GMM-7550/gmm7550-hardware/doc/gmm7550_preview_side_2022-03-09.png

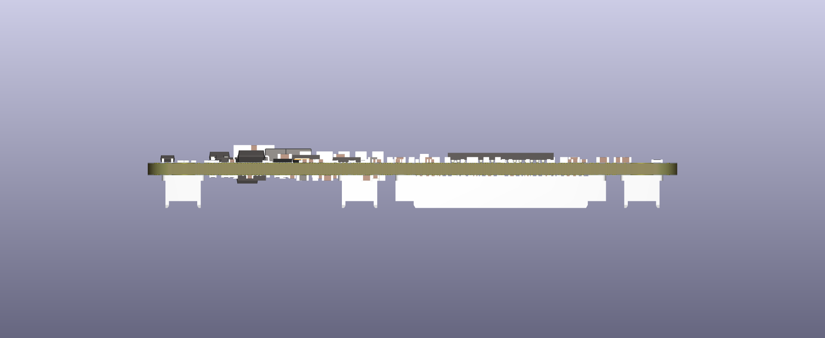
doc/gmm7550_preview_side_2022-03-09.png
