GMM-7550/gmm7550-hardware/doc/GMM-7550_preview_2020-10-01.png

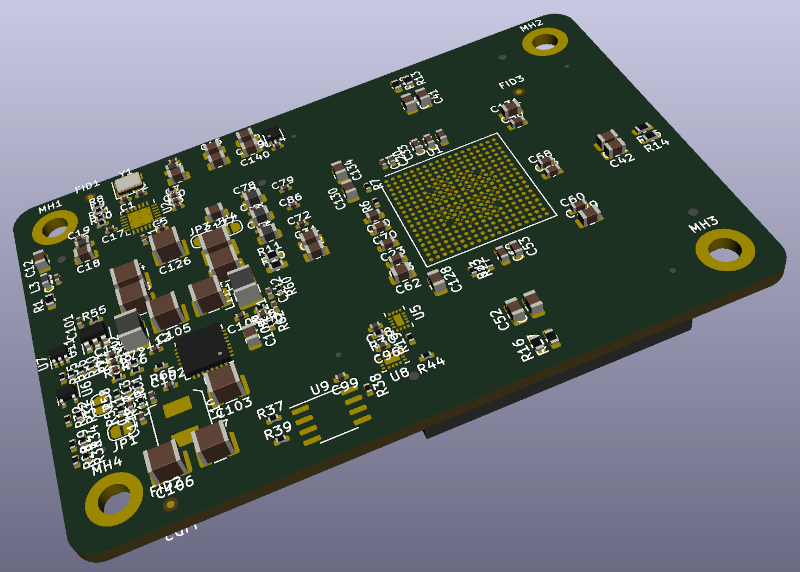
doc/GMM-7550_preview_2020-10-01.png
