GMM-7550/gmm7550-hardware/doc/hat-gmm7550_preview_2022-02-13.png

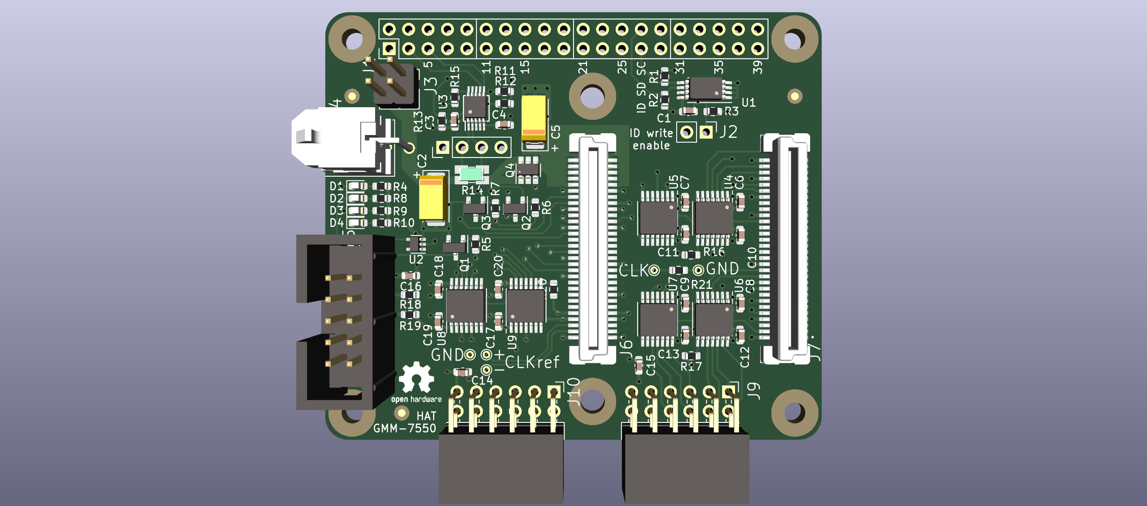
doc/hat-gmm7550_preview_2022-02-13.png
