GMM-7550/gmm7550-hardware/doc/usb3-gmm7550_1.0_2025-10-10.png

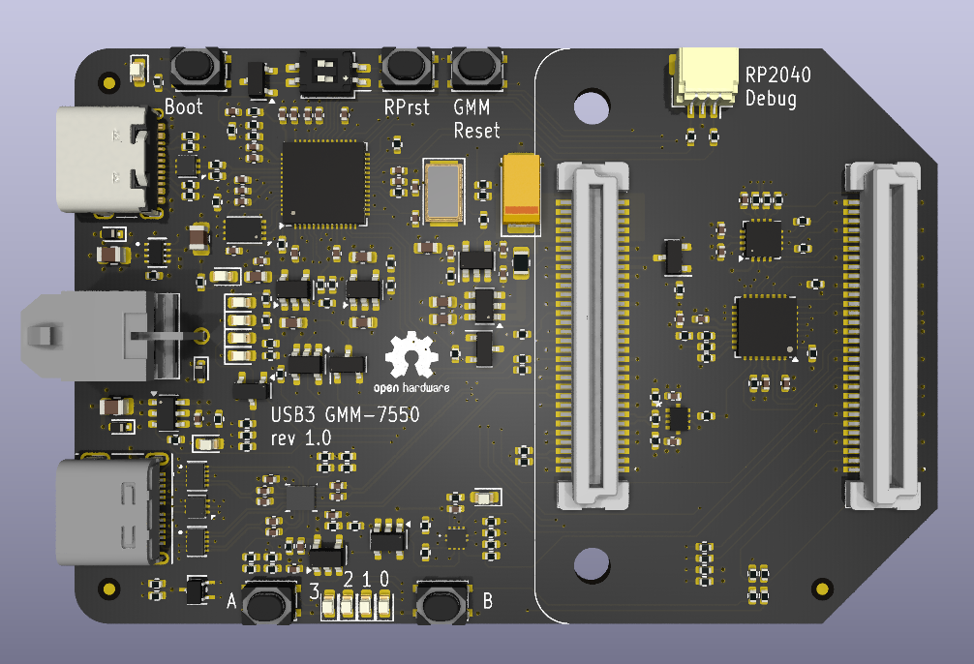
doc/usb3-gmm7550_1.0_2025-10-10.png
