GMM-7550/gmm7550-hardware/doc/usb3-gmm7550_preview_2025-08-17.png

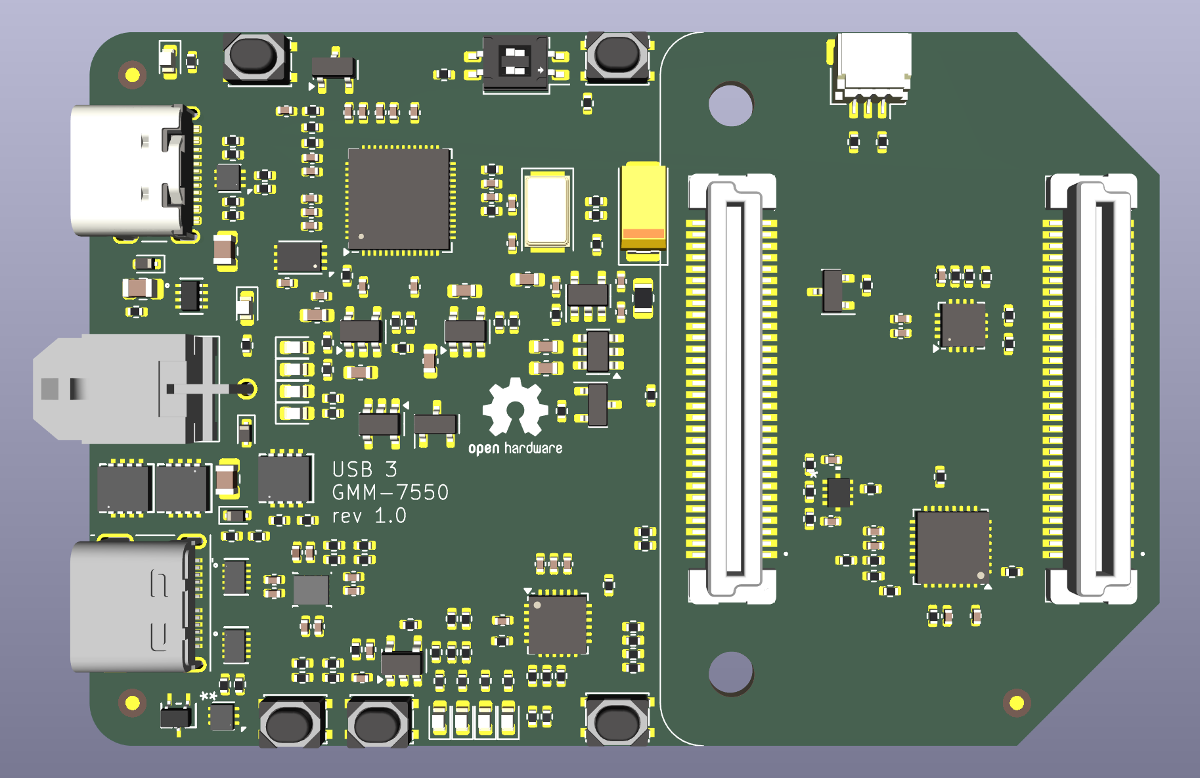
doc/usb3-gmm7550_preview_2025-08-17.png
