GMM-7550/gmm7550-hardware/usb3-gmm7550.kicad/production/usb3-gmm7550_1.0_2025-10-16/pdf/usb3-gmm7550-User_Drawings.pdf

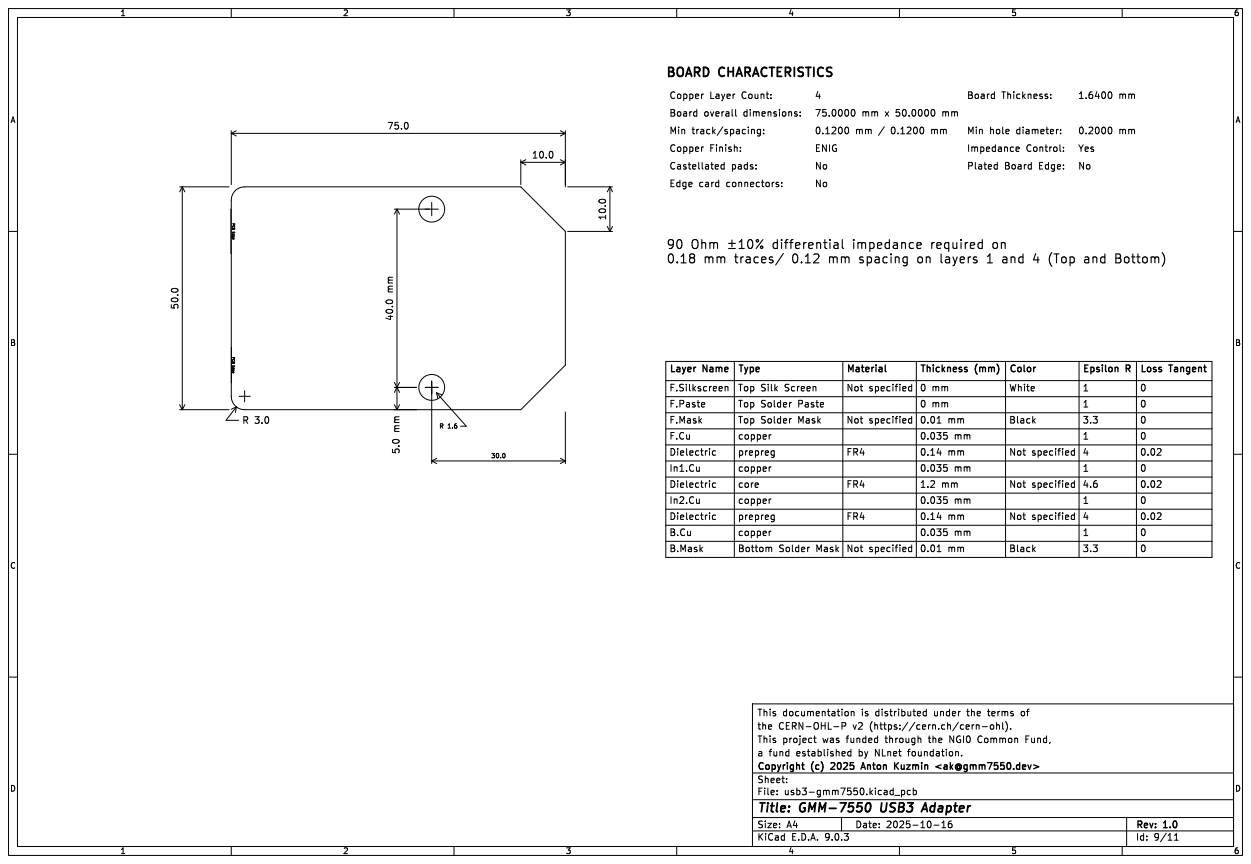
[picture p27: page 1]

Copper Layer Count: Bottom Solder Mask F.Paste B.Cu

Not specified Dielectric | 0 mm | Color 0.035 mm | Epsilon R 1

Layer Name F.Silkscreen | Top Silk Screen | Material prepreg | Thickness | (mm) | | 3.3 | 0 Type 0.02 F.Cu 0 0

prepreg | | 0.14 mm | | | | 0 Black
copper | FR4 Not specified | 0.035 mm | | Black Not specified | 1 | 0.02

In2.Cu | | | 0.035 mm | | | 0 Not specified Not specified 0

copper | | 0.14 mm | | 4 | 0.02

0.035 mm
0.01 mm

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

USB3 Adapter File: usb3-gmm7550.kicad_pcb Sheet: Copyright (c) 2025 Anton | Kuzmin <ak@gmm7550.dev> Id: 9/11 Title: GMM-7550
